seeimadeit/z80/initial/pic18f24q10_clock.X/main.c

/**
  Generated Main Source File

  Company:
    Microchip Technology Inc.

  File Name:
    main.c

  Summary:
    This is the main file generated using PIC10 / PIC12 / PIC16 / PIC18 MCUs

  Description:
    This header file provides implementations for driver APIs for all modules selected in the GUI.
    Generation Information :
        Product Revision  :  PIC10 / PIC12 / PIC16 / PIC18 MCUs - 1.81.6
        Device            :  PIC18F24Q10
        Driver Version    :  2.00
*/

/*
    (c) 2018 Microchip Technology Inc. and its subsidiaries. 
    
    Subject to your compliance with these terms, you may use Microchip software and any 
    derivatives exclusively with Microchip products. It is your responsibility to comply with third party 
    license terms applicable to your use of third party software (including open source software) that 
    may accompany Microchip software.
    
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
    IN NO EVENT WILL MICROCHIP BE LIABLE FOR ANY INDIRECT, SPECIAL, PUNITIVE, 
    INCIDENTAL OR CONSEQUENTIAL LOSS, DAMAGE, COST OR EXPENSE OF ANY KIND 
    WHATSOEVER RELATED TO THE SOFTWARE, HOWEVER CAUSED, EVEN IF MICROCHIP 
    HAS BEEN ADVISED OF THE POSSIBILITY OR THE DAMAGES ARE FORESEEABLE. TO 
    THE FULLEST EXTENT ALLOWED BY LAW, MICROCHIP'S TOTAL LIABILITY ON ALL 
    CLAIMS IN ANY WAY RELATED TO THIS SOFTWARE WILL NOT EXCEED THE AMOUNT 
    OF FEES, IF ANY, THAT YOU HAVE PAID DIRECTLY TO MICROCHIP FOR THIS 
    SOFTWARE.
*/

#include "mcc_generated_files/mcc.h"

/*
                         Main application
 */
volatile int counter=1;
void main(void)
{
    // Initialize the device
    SYSTEM_Initialize();

    // If using interrupts in PIC18 High/Low Priority Mode you need to enable the Global High and Low Interrupts
    // If using interrupts in PIC Mid-Range Compatibility Mode you need to enable the Global and Peripheral Interrupts
    // Use the following macros to:

    // Enable the Global Interrupts
    INTERRUPT_GlobalInterruptEnable();

    // Disable the Global Interrupts
    //INTERRUPT_GlobalInterruptDisable();

    // Enable the Peripheral Interrupts
    INTERRUPT_PeripheralInterruptEnable();

    // Disable the Peripheral Interrupts
    //INTERRUPT_PeripheralInterruptDisable();
 
    /*
     divider    value   clock
     512    0x69    3.9khz
     256    0x68    7.8khz
     128    0x67    15.6khz
      64    0x65    31.2khz
      32    0x64    62.5khz
      16    0x63    125khz
       8    0x62    250khz
       4    0x61    500khz
       2    0x60    1Mhz
       1    0x59    2Mhz
     */
 
    int flag=0x66; // default 31
    while (1)
    {
        // Add your application code
        if (counter)
        {
               OSCCON1 = flag;
               flag--;
               if (flag==0x5f) flag = 0x69;

           
               counter=0;
        }
     
            
    
    }
}


void IOCCF5_DefaultInterruptHandler(void){
    // add your IOCCF5 interrupt custom code
    // or set custom function using IOCCF5_SetInterruptHandler()
    LED_Toggle();
    counter=1;
}
/**
 End of File
*/
